DaleMitchell/STM-Remote-Knob-Controller/Images/GUI-screenshot-about.png

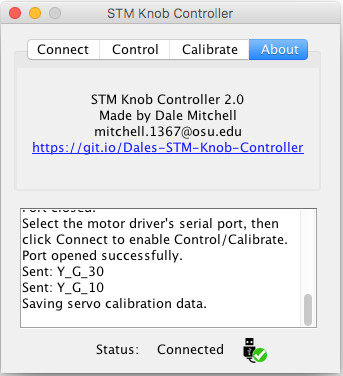
Images/GUI-screenshot-about.png
