DaleMitchell/STM-Remote-Knob-Controller/Images/knobs-attached-to-motors.jpg

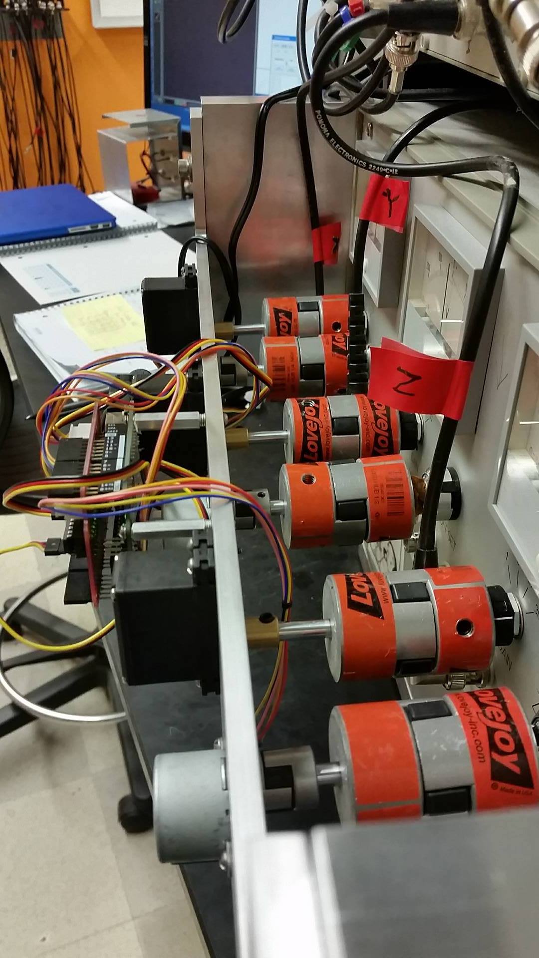
Images/knobs-attached-to-motors.jpg
