DaleMitchell/STM-Remote-Knob-Controller/Images/STM-imaging.jpg

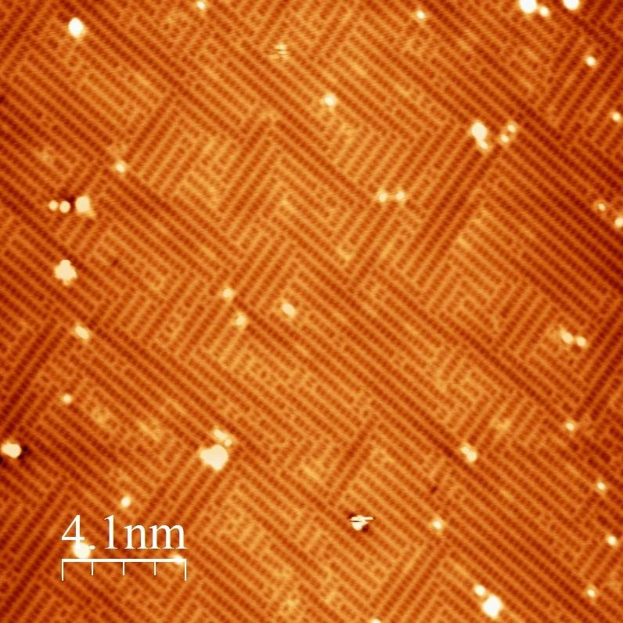
Images/STM-imaging.jpg
