DaleMitchell/STM-Remote-Knob-Controller/Images/GUI_screenshot_calibrate.png

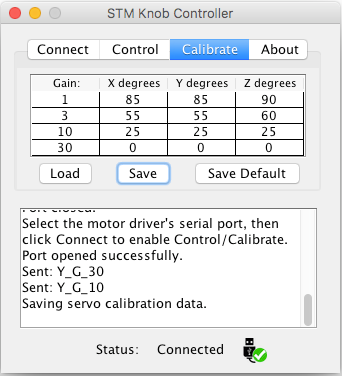
Images/GUI_screenshot_calibrate.png
